rickethyo/TurnHub/Documentation/engineering/PLAYERS_AND_ACCOUNTS.md

# Players, Profiles and Accounts

Profiles, sign-in, joining a table from a phone or a Sigil, permissions and
moderation. Storage keys are in [Storage and Recovery](STORAGE_AND_RECOVERY.md);
HTTP routes are in `protocol/http-v1.md` and the route table in
`Atlas/src/web_api.cpp`.

## Profiles and sign-in

- A profile is a person: ID, name, a PIN (4-8 digits) or password (8-64
  UTF-8 bytes, no control characters), statistics and preferences. Both
  secrets travel in the same `pin` field, use the same hash
  (`profilePinHash`, a single SHA-256 over profile ID and secret) and the same
  login limiter. At most 64 profiles; new profiles need a name and secret.
- Anyone on Atlas's network can register. Signing in gives a native client
  session token (RAM only, eight-hour inactivity expiry, sent in the
  `X-TurnHub-Token` header, never in URLs). Changing the secret revokes the
  profile's other tokens. Logout removes authorization, not the participant.
- Signing in does not join the table. The authenticated profile, never a
  client-supplied player field, decides what a session may control.
- The Android app can keep one profile's secret in the Android Keystore,
  unlocked by fingerprint, face, screen lock or an app PIN, and signs in
  whenever it connects (Android 11+, `Android/README.md`). Real passkeys don't
  fit an offline Atlas (WebAuthn needs a domain name and a trusted
  certificate).

## Joining a table

- One profile has **at most one participant** at the table. Two phones and a
  Sigil may all control that participant; statistics count once.
- **Phones** join with `POST /api/session/join` and can form a whole table
  with no Sigils: pick a starter, start, play, finish, rematch.
- **Sigils** join through the **profile picker** (`profile_picker.cpp`, RAM
  browsing state only). The page lists Guest, then saved profiles, three to
  a page. E-ink: each name has a fixed key (Up/Right/Down), the click shows
  more names, Left goes back. OLED: the same page as a scrolling list. Words
  mark special rows: "no profile" (Guest), "phone sign-in" (the owner turned
  off physical use without a PIN and has no signed-in phone), "at table:
  attach" (already playing from a phone; choosing it attaches this Sigil to
  that participant). Archived or moderated profiles and profiles on another
  Sigil are not listed. Names that would look the same on a Sigil (the
  same name, or the same first 12 characters) are numbered in profile ID
  order, "Sam 1" and "Sam 2", cut to fit (2026-10-06). The picker closes after a minute idle, at game start,
  or when the Sigil joins another way.
- **Use this seat** (the app’s Players tab):
  `POST /api/session/request` with `module` and `slot`, then poll
  `GET /api/session/poll?id=` while the player chooses **Link phone** on that
  Sigil within 30 s. Signed out, approval signs the phone in to the seat's
  profile, and only for a profile without a PIN (a Sigil press proves
  possession, not the secret). Signed in, it attaches that Sigil seat to the
  signed-in profile. The app signs in from its profile list. In a lobby its Paired Sigils list
  can also request attachment of an empty seat A, with the same physical
  confirmation and server validation.
- **First phone sign-in of a PIN-less profile** (owner request 2026-10-07):
  `POST /api/session/login` for a profile with no secret saves the given PIN
  or password as its secret and signs in (log `ATLAS|PROFILE|PIN_SET_AT_SIGN_IN`).
  The app asks for it twice; from then on it is checked as usual. Anyone at
  the table can already seat a PIN-less profile from a Sigil or the tablet,
  so claiming it from a phone grants nothing new.
- **Seat B** on a shared Sigil uses the same picker (**Add seat B**); Guest
  adds seat B directly. `PickProfile` with slot 2 adds the seat and binds the
  profile in one step.
- Attachment and profile choice happen in the lobby, with one exception
  (owner request 2026-10-07, *Experimental: host-tested*): during a running
  or paused game a Sigil outside it offers **Join** while some player in the
  game has no Sigil (seated from a phone or the tablet). Its picker then lists
  only those players (no Guest), and choosing one moves that player onto the
  Sigil with their place, life and clock (`GameEngine::replaceController`).
  Nobody new joins mid-game until venue lobbies, and a participant that
  already has a physical controller is never silently moved.
- Seat bindings are temporary (RAM): released when the seat leaves (the
  Sigil's Leave, Drop seat B, a phone leaving for a profile seated on a
  Sigil, a Game Master removal), at Reset and on restart. They survive Game
  Over so Sigils can name the winner, and Rematch restores them. A seated
  Sigil that reboots keeps its profiles.
- **Turn order** is set on the Atlas touchscreen in the lobby by tapping a
  player chip: Earlier/Later (`MoveSeat`) and, on a shared Sigil, B left or
  B right (`SetSeatSide`). Any player may do it, and so may a table tablet
  (Earlier/Later, 2026-10-07); a phone may not.
  Starter, participants and bindings stay with their physical seats, and
  recovery restores A/B and B/A pairs.

## Tablet mode (2026-10-06)

*Experimental: host-tested, not yet played on hardware.* One shared tablet or
phone lies in the middle of the table, split into a panel per player that
faces their seat (Android app, Game → Open tablet mode, `ui/tablet/`).
The app renders `/api/v1/state` and sends `/api/tablet/*` requests; it keeps
the screen on and hides system bars during play. Browser tablet mode is retired.
The game selector follows Atlas’s venue list. A shared-tablet switch keeps its
players seated in their original game. State/name caches and local staged edits
reset when games change; queued offline changes include the venue game, boot
and participant identity. Native raw table actions include `expectedGame`; Atlas
rejects a stale selected-game context before dispatching the semantic action.

- **Turning it on.** A signed-in account activates tablet mode from Game.
  With the table-code setting off it activates directly; when on, prove table
  presence with `purpose=tablet` and the Atlas code, unless the account has
  Tablet access. Successful `POST /api/tablet/enable` revokes this device's
  personal token and returns a fresh RAM-only shared-tablet credential. Its
  profile ID is empty, its name is Shared tablet, and it has no personal or
  Admin permissions. It cannot join as a player, edit profiles, upload artwork,
  inspect private preferences/statistics or administer Atlas. The route allowlist
  permits game/state/seats/profile-list/artwork reads, tablet actions, game
  selection and logout. Existing player seats and other phones stay independent.
  Closing or leaving tablet mode revokes the grant and leaves the app signed
  out, including local exit while disconnected. Remote sessions expire after
  eight idle hours or restart. No personal login is restored on exit.
- **Seating.** In the lobby the tablet adds players: a new name creates a
  profile with no PIN (names are unique, ignoring case); an existing profile
  follows its owner's PIN choice below, else the tablet asks for its PIN
  (rate limited like a sign-in). Seated players join as browser controllers,
  so a Sigil can then attach to any of them through its picker ("at table:
  attach") and a phone can sign in to the same participant.
- **Turn order.** The tablet lobby's arrows move a seat earlier or later
  (`move-earlier`/`move-later`, `MoveSeat` with the `TableTablet` origin);
  panels sit clockwise in that order. The game's order is fixed once it
  starts. Claim the win and Concede sit at the top of each panel's More.
- **Acting for a seat.** Every panel action names the seat (`module`, `slot`
  from `/api/v1/state`) and goes through the same seat callbacks and Intents
  a phone uses (`web_tablet_api.cpp`). Atlas still decides: a seat changes
  only its own life, records only Commander damage it received, only the
  active player passes or claims a win, and win confirmations go to the
  confirming seat. Statistics are recorded per profile as for any game.
- **Paused decisions:** tablet clients keep the central pause overlay closed
  during a win claim so the scheduled player's panel can Confirm or Deny.
  Resume is offered only for an ordinary pause. Elimination selection directs
  the table to the existing Atlas/Sigil controls instead of offering Resume.

## Owner policy

Each profile owner chooses, in the portal or app (`POST /api/session/policy`):

- **Allow Sigil and tablet use without a PIN** (`allowPhysicalWithoutPin`).
  Off means a Sigil or a table tablet can seat that profile only while the
  same profile has a live phone session, or (tablet only) after its PIN is
  typed on the tablet. Turning it off needs a saved secret. Existing participation continues if the policy
  changes or the session expires.
- **Hide stats without authentication.** Controls visibility only; statistics
  always accumulate. Atlas enforces it before serializing anything.

Missing records keep physical play allowed and hide unauthenticated stats.
Anyone at the table can see the list of profile names, as in the portal's
sign-in list.

## Permissions

| Permission | Allows |
|---|---|
| Admin | Account permissions, device names, network settings, firmware and portal updates, pairing confirmation and forget, factory reset, Return table to lobby, speaker volume |
| Game Master | Force pass (logged as a master pass), nudge mute; optional sub-permissions **reset connections** and **remove from game** |
| Developer | Developer page, diagnostics and the RAM log download (`GET /api/diagnostics/log`) |
| Tablet access | Turns on tablet mode without a table presence code (bit 32; needs no other role) |

A normal account has none. Permissions combine freely and are checked on
Atlas for every protected request. Privileged accounts can't remove their
secret. **There is no table host** (2026-09-25): any seated player may start,
pick the starter, change next-game settings, rematch or reset.

**First Admin.** On a new Atlas the app's setup or the portal's banner lets a
signed-in account with a secret claim the first Admin, after proving
presence (below). Neither a name nor first registration grants privileges.
The first Admin can't be demoted.

**Presence at the table** (`front_panel.cpp`). Protected device actions need
proof that the account holder is at the table: the account asks for a code,
the Atlas screen shows a six-digit code and a QR code for that account only
for 90 s (`PRESENCE_CODE_MS`), and entering or scanning it verifies the
account for 10 minutes (`PRESENCE_GRANT_MS`). Five wrong codes cancel it;
**Cancel** on the screen removes a code nobody asked for; **Stop** in Device
Settings ends a grant early. Without it the request gets
`403 {"presenceRequired": true}` and the client starts the code flow. It is
needed for the first Admin, network settings, device names, firmware and
portal updates, pairing confirmation, Return table to lobby and factory reset.

**The table code is optional** (2026-10-08, after testers found the code on
every update a reason not to use TurnHub). It is **off by default**: every
signed-in account counts as at the table, so the account permission alone
decides (an Admin for everything above), and firmware still installs only
when signed and the same or newer. An Admin turns it on in Device Settings
(portal, basic portal or app), saved in NVS as `tcode`
(`table_code_setting.h`, Intent `ConfigureTableCode`). Turning it off again
needs a code that Admin actually entered, so an Admin elsewhere on the Wi-Fi
cannot quietly drop the extra step. While it is off the Atlas screen's Wi-Fi
QR code also shows a private password without a code.

## Moderation

Game Master actions go through the `Moderate` Intent, which re-checks
permission and target state:

- **Force pass** acts at once, within the normal pause and decision rules.
- **Reset connections** revokes the target's sessions and pending claims and
  suspends its Sigil controls until a PIN sign-in. Seat, life and game state
  stay. A shared Sigil is suspended as a unit.
- **Remove from game** also leaves the lobby or eliminates the participant
  through the concession flow (open decisions finish first; a primary seat
  with a seat B removes B first). The account and statistics stay.
- **Nudge mute** stops that account sending nudges (`NudgePlayer` is refused).

Both disconnecting actions need the target to have a secret. Connection
resets and removals are counted (`o<profileId>`), saved before acting
(a storage failure rejects the action), and shown only to the account's own
PIN-verified session, never to Admins, Game Masters, seats, Sigils or
exports.

Archived accounts stay visible to Admins at the bottom of the account list,
can be restored, and are hidden from Game Master tools.

## Not done yet

- A slower salted hash (PBKDF2 via mbedTLS) for PINs and passwords, and a
  larger NVS partition, since today's 20 KB likely fits only about 20 profiles
  rather than 64. Both are parked together in
  [Staged Changes](STAGED_CHANGES.md), "Parked: storage batch".
- Future LCD artwork transfer/cache and final ESP32-S3 screen layouts.
- Per-Sigil startup choice (last profile or picker).
- Moderation from the Atlas Player screen.

## Verification

Host scenarios run the real HTTP handlers, Intent handlers and engine:
registration and login (PIN and password), hardware-free games, duplicate-join
refusal, concurrent sessions, logout and re-login, PIN throttling and
revocation, mixed attachment, the picker for both seats and policies,
permissions, presence codes, moderation and counter privacy. Phone-only
games, phone plus Sigil on one player and persistence across reboots are
verified in use (owner, 2026-10-02).

## Standalone device identity and optional import

Android local players have their own UUIDs, independent of Atlas profiles.
Adding a name creates a player; selecting a saved player reuses the local ID.
Equal names remain separate. Completed matches snapshot identity/name and keep
local statistics independent of Atlas totals. History/import state belongs to
Android's local library; see [Android](../../Android/README.md) for the schema.

Optional import requires explicit per-match choices for all players on a
specific `(atlasId, profileId)` destination. Linking never renames/replaces a
local player or rewrites historical match facts. No typed-name, cached-name or
cross-Atlas matching exists. Pending mappings are frozen for retry, imported
matches cannot be submitted again by the app, and rejected records/reasons stay
visible for explicit review. Atlas validates destination hardware identity and
all exact profile identities before crediting a new record. Existing session
sign-in is still required; profile linking does not itself grant permissions.
See [import contract](../../protocol/http-v1.md#standalone-tablet-game-import-2026-10-07).

## Player artwork (2026-10-10)

*Implemented; host/build validation recorded in COLLABORATION.md; physical
acceptance pending.* Preset keys and IDs stay stable. Android uses scalable
vector masters in `design/avatars`; Atlas uses generated 64-pixel alpha masks
area-filtered into its current slot. Frozen Sigils retain their existing assets.

My account → Personalization accepts a phone-local JPEG/PNG/WebP (up to 20 MiB
and 32 megapixels). Bounded decode honors EXIF orientation, crop sliders choose
zoom and position, and Preview displays the final compressed image plus
provisional 64/128-pixel LCD previews. The phone flattens transparency on white
and produces a baseline RGB JPEG, 512 square pixels and at most 48 KiB. The
original is never uploaded. Upload/replace stores pending art on Atlas's SD;
Admin review in Players → People → person approves or rejects the specific
revision. Pending art is private to that player and Admins; approval selects it
for public app/tablet/Atlas display. Pending replacement retains approved art.
None/presets may be selected without deleting approved artwork; Remove uploaded
image removes pending/approved artwork and selects None. Refresh image approval
reloads the profile after review. Current Sigils render their ordinary fallback.

SD unavailability fails saves visibly and falls back safely for play. A checksum
or decode failure displays a neutral fallback. Artwork is outside game-state
polling; immutable image paths are cached per connection/game. Names, life totals
and controls remain separate from decorative artwork. The master is suitable for
future LCD layouts; those firmware targets and their radio transfer are pending.
