rickethyo/TurnHub/Documentation/legal/DEPENDENCY_TRACKER.md

# TurnHub Dependency and IP Tracker

This is the working tracker for third-party software, assets, trademarks, externally sourced design material, and other IP that may create attribution, licensing, or release obligations.

The goal is simple: know what entered the project, where it came from, how it is used, and what must happen before distribution.

## Status legend

- **GREEN** - permissive or tool-only dependency with straightforward obligations.
- **YELLOW** - compatible in principle, but distribution details or exact obligations still need confirmation.
- **RED** - strong copyleft, unknown license, noncommercial restriction, incompatible terms, or another issue that must be resolved before production distribution.
- **N/A** - reference/trademark/design item rather than a software license.

## Current software dependencies

| Item | Version/source currently known | Used by | License | Ships with product? | Status | Required action |
| --- | --- | --- | --- | --- | --- | --- |
| Arduino-ESP32 | PlatformIO `espressif32`, Arduino framework | Atlas + Sigil | LGPL-2.1 | Yes, firmware build | YELLOW | Confirm exact release version/components and satisfy LGPL distribution/relinking/source obligations for the chosen firmware distribution model. Preserve notices. |
| GxEPD2 | `zinggjm/GxEPD2`, current PlatformIO dependency | Sigil e-ink | GPL-3.0 | Yes if current Sigil firmware ships | RED | Decide before production whether to comply with GPLv3 for the resulting firmware or replace with a suitably licensed display driver. Legal review before commercial release. |
| Adafruit GFX Library | Transitive GxEPD2 / SH110X dependency | Sigil e-ink and OLED graphics | BSD-style | Yes if linked into shipped firmware | GREEN | Preserve copyright, conditions, and disclaimer in release notices/materials as required. |
| LovyanGFX | `lovyan03/LovyanGFX@1.2.30` (PlatformIO) | Atlas TFT (E32R28T) | FreeBSD (BSD-2-Clause) for LovyanGFX. Bundled Adafruit (BSD) and Bodmer (FreeBSD) code carries its own notices | Yes, Atlas firmware | GREEN | Preserve the combined notices in `license.txt` in release materials. Atlas uses LovyanGFX's DejaVu fonts (Bitstream Vera-style license) and glcd font, plus its own Brass fonts (Cinzel/Oswald, row below); do not use the bundled GNU FreeFont `Free*` fonts (GPL with font exception) without review. |
| Cinzel and Oswald fonts (Brass display theme) | Cinzel 2.000 static Bold/Black ([NDISCOVER/Cinzel](https://github.com/NDISCOVER/Cinzel)) and Oswald 4.103 SemiBold ([googlefonts/OswaldFont](https://github.com/googlefonts/OswaldFont)), both fetched from Google Fonts; rendered to bitmaps by `tools/fonts/make_fonts.py` into `Atlas/include/brass_fonts.h` and `Sigil/include/brass_fonts.h` (2026-09-29). The TTFs are not committed | Atlas TFT, Sigil e-ink and OLED text | SIL Open Font License 1.1 (text and copyright lines in `tools/fonts/OFL.txt`) | Yes, embedded bitmaps in both firmwares | GREEN | Embedding in firmware is allowed. Keep `tools/fonts/OFL.txt` with the source and include its copyright lines and license in release notices. Never sell the fonts by themselves. Neither font declares a Reserved Font Name. |
| Inter and Cinzel variable fonts (V1 design system) | Inter 4 `Inter[opsz,wght].ttf` and Cinzel `Cinzel[wght].ttf` from [google/fonts](https://github.com/google/fonts) (`ofl/inter`, `ofl/cinzel`), fetched 2026-10-02, subset to Latin with fontTools; committed as `design/fonts/*.ttf` and `*.woff2` (see `design/README.md`) | Android app, and Inter bitmap text in Atlas/Sigil firmware (`tools/fonts/make_modern_fonts.py`, 2026-10-09) | SIL Open Font License 1.1 (`design/fonts/OFL-Inter.txt`, `design/fonts/OFL-Cinzel.txt`) | Yes, APK and firmware bitmaps | GREEN | Ship the OFL texts with app open-source notices and firmware notices. The admin portal uses system fonts. Subsetting creates a Modified Version; neither font declares a Reserved Font Name, so the family names may stay. Never sell the fonts by themselves. |
| Adafruit SH110X | `adafruit/Adafruit SH110X@2.1.15`, [upstream](https://github.com/adafruit/Adafruit_SH110x) | Optional Sigil OLED environment only | BSD-3-Clause ([license](https://github.com/adafruit/Adafruit_SH110x/blob/master/license.txt)) | Yes if OLED firmware ships | GREEN | Preserve upstream copyright, license, disclaimer and required source notices in release materials; the vendor splash is disabled in the build. |
| Adafruit NeoPixel | `adafruit/Adafruit NeoPixel@1.15.5`, [upstream](https://github.com/adafruit/Adafruit_NeoPixel) | Sigil E-ink build (`sigil` env) status ring only | LGPL-3.0 ([license](https://github.com/adafruit/Adafruit_NeoPixel/blob/master/COPYING)) | Yes if E-ink Sigil firmware ships | YELLOW | Statically linked, so LGPL-3.0 requires letting recipients relink against a modified library (e.g. provide object files or the full source) and preserving notices. Covered by the same pre-release review as GxEPD2 (GPL-3.0) in the same firmware. |
| Mbed TLS | 2.28.7, bundled inside Arduino-ESP32 (framework-arduinoespressif32 2.0.17); no separate PlatformIO dependency | Atlas + Sigil secure link (X25519, AES-128-CCM, HMAC-SHA256; `shared/include/secure_link_mbedtls.h`, 2026-09-28) | Apache-2.0 (upstream also offers GPL-2.0-or-later; Espressif ships it under Apache-2.0) | Yes, linked into both firmwares | GREEN | Preserve the Apache-2.0 license and NOTICE in release materials with the other Arduino-ESP32 notices. TurnHub calls its primitives only; no mbedTLS source is copied into the repository. The RFC test vectors in `secure_link.h` are published values from RFC 7748, 4231 and 3610. |
| Adafruit BusIO | Transitive GFX / SH110X dependency | Sigil graphics bus support | MIT ([license](https://github.com/adafruit/Adafruit_BusIO/blob/master/LICENSE)) | Yes if linked into shipped firmware | GREEN | Preserve copyright and license notice. |
| PlatformIO Core | Build environment | Development | Apache-2.0 | No, currently build tooling only | GREEN | Track tool version for reproducibility. No product notice expected unless redistributed. |
| Python `cryptography` | 46.0.7 (pip in CI; locally the copy bundled with PlatformIO's esptool) | `tools/firmware/thfw.py`: signs and checks OTA packages (2026-09-29) | Apache-2.0 or BSD-3-Clause | No, developer and CI tooling only | GREEN | Not shipped. The signatures it makes are verified on the devices by Mbed TLS and in the app by `java.security`. |
| GitHub Actions: checkout, setup-python, setup-java, upload-artifact | Official `actions/*` repositories; exact commit revisions in `.github/workflows/ci.yml` | Development CI only | MIT (upstream `LICENSE` in each action repository) | No, not embedded in firmware or APK | GREEN | Preserve upstream notices if action code is ever redistributed. Workflow invokes the actions without copying their implementation into TurnHub. |
| GitHub Action: r0adkll/upload-google-play | `r0adkll/upload-google-play` v1.1.5, pinned to commit `e738b9dd8f2476ea806d921b64aacd24f34515a5` in `.github/workflows/ci.yml` | Development CI only: publishes master's Android bundle to Play internal testing | MIT (upstream `LICENSE`) | No, not embedded in firmware or APK | GREEN | Receives the Play service account key at run time; keep it pinned to a reviewed commit. |
| wokwi-ws29v2-custom-chip | `bonnyr/wokwi-ws29v2-custom-chip` release v0.0.5 `chip.zip` (`chip.wasm` SHA-256 `6f59d1873e3faa07a018a088f61b1ffff6a8bcfebf7925eadd7e2082dd318d9d`), vendored as `Sigil/wokwi/chips/epaper-2in13.chip.wasm` with a TurnHub `chip.json` (2.13" geometry) | Sigil Wokwi simulation only | MIT (copy in `Sigil/wokwi/chips/LICENSE-wokwi-ws29v2-custom-chip.txt`) | No, development simulation only | GREEN | Keep the license file with the binary. Not linked into firmware. |
| org.json (JSON-java) | `org.json:json:20260814`, Android `testImplementation` only | Android JVM unit tests (the app itself uses Android's built-in `org.json`) | Public Domain (per its Maven POM) | No, test classpath only | GREEN | None while test-only. Re-review if it ever moves to an `implementation` dependency. |
| AndroidX CameraX (`camera-camera2`, `camera-lifecycle`, `camera-view`) | `androidx.camera:*:1.5.0` | Android app: Admin-code QR scanner preview | Apache-2.0 | Yes, Android APK | GREEN | Include the Apache-2.0 license and any NOTICE text in the app's open-source notices. Camera use is optional and asked for only when the player taps Scan. |
| ZXing core | `com.google.zxing:core:3.5.3`, [upstream](https://github.com/zxing/zxing) | Android app: on-device QR decoding (no network) | Apache-2.0 | Yes, Android APK | GREEN | Include the Apache-2.0 license and NOTICE in the app's open-source notices. |

## Platform/toolchain follow-up

Optional Windows native-test compiler: PlatformIO package
`platformio/toolchain-gccmingw32` 1.50100.0 (GCC 5.1.0), used by
`Atlas/tests/host/run-gcc.ps1`. Installed package provenance is recorded in its
`package.json`; component license texts are in its `licenses/` directory.
This is development-only tooling, not linked into ESP32 firmware. Compiler and
native test binaries are not committed or distributed. Review the package's
component/runtime redistribution terms before distributing either; MSVC remains
an alternative via `run.cmd`.

The high-level rows above are not yet a complete software bill of materials. Before release, generate the dependency list from the exact production builds and inventory:

- Espressif SDK/framework components pulled into Atlas firmware.
- Espressif SDK/framework components pulled into Sigil firmware.
- Any binary blobs, bootloaders, partition tools, OTA components, crypto libraries, or other linked code included by the toolchain.
- Android application dependencies once the native client is created.
- Any future BLE, QR, image, persistence, networking, or serialization libraries.

## Assets and externally sourced material

| Item | Current state | Status | Rule |
| --- | --- | --- | --- |
| Web UI fonts | Admin portal: system fonts; Android app: Inter and Cinzel, recorded under software dependencies | GREEN | Keep the OFL texts with app notices; the portal embeds no web fonts. |
| Web UI icons/images | No external icon/image package identified in current ESP32 portal | GREEN | Do not paste icons/art from another product. Record any future asset pack before use. |
| V1 icon set and brand mark | Original line icons drawn for TurnHub on 2026-10-02 (`design/icons/*.svg`) and an original turn-arrow mark; no third-party icon set | GREEN | Keep new icons original; record the source of any icon that is not. |
| Sigil display graphics | Programmatic geometry (gears, rivets, gauges) plus the Cinzel/Oswald bitmap fonts recorded above; no third-party art identified | GREEN | Continue using original/programmatic assets unless a licensed source is recorded. |
| Sounds/tones | Programmatic buzzer tones; no sampled third-party audio identified | GREEN | Record any future audio file, sound pack, or melody source and license. |
| CAD/enclosure files | No external production enclosure asset recorded in this tracker | GREEN | If a downloaded 3D model is used or modified, record source and model license before committing/shipping it. |
| Schematics/reference designs | No third-party schematic copied into the production tree is currently recorded | GREEN | Record vendor/reference-design source and applicable terms if incorporated. |

## Trademark and compatibility references

| Reference | Current use | Status | Required action |
| --- | --- | --- | --- |
| Magic: The Gathering / MTG | Game profile/compatibility wording in documentation and legacy UI | N/A | Keep use descriptive. Avoid logos, card art, mana symbols, card frames, or implication of affiliation. Review commercial wording before launch. |
| Commander / MTG Commander | Game profile and commander-damage terminology | N/A | Same as above. Review exact naming/disclaimer strategy before public commercial release. |
| Yu-Gi-Oh! | Game profile/compatibility wording | N/A | Keep descriptive and avoid branded visual assets or implied endorsement. Review before launch. |

## Open IP/legal tasks

- [ ] Resolve GxEPD2 GPLv3 strategy before any commercial Sigil firmware distribution.
- [ ] Correct the placeholder `[year] [fullname]` in the root `LICENSE.txt` and confirm the intended license scope.
- [ ] Produce an exact production SBOM/dependency manifest from Atlas and Sigil release builds.
- [ ] Add complete required upstream license texts/notices to the release package.
- [ ] Review trademark compatibility wording before Kickstarter, retail packaging, app-store publication, or paid promotion.
- [ ] Add Android dependencies here as soon as the native project is generated.
- [ ] Perform a final third-party asset audit before public release.

## Change log

### 2026-09-28 (GitHub Actions)

Recorded the four official GitHub actions used for checkout, language setup and
development artifact retention. They run on GitHub-hosted build machines and do
not add a device/runtime dependency.

### 2026-09-25 (Sigil status ring)

Added Adafruit NeoPixel (LGPL-3.0) for the E-ink Sigil's Jewel 7 status ring.
No third-party code was copied into the tree.

### 2026-09-24 (Sigil OLED scaffold)

Added the optional SH110X driver, recorded BusIO and extended the GFX usage
record. No third-party implementation code or photo was copied into the tree.

### 2026-09-24 (Atlas display)

Added LovyanGFX for the Atlas E32R28T TFT, and recorded the font restriction.

### 2026-09-24

Added the test-only `org.json:json` dependency introduced with the Android live-Atlas integration. The broader Android dependency inventory (AndroidX, Compose, coroutines, JUnit) remains the open task above.

### 2026-09-19

Initial tracker created from the current `intent-android-foundation` branch. Known direct dependencies and current game-name compatibility references were inventoried. GxEPD2 was marked RED for production review because the current Sigil firmware directly uses it under GPLv3.

### Artwork build tools (2026-10-10)

CairoSVG 2.8.2 (LGPL-3.0-or-later) and Pillow 11.3.0 (HPND/Pillow license)
are development-only rasterization tools pinned in `tools/artwork-requirements.txt`.
They generate alpha masks from TurnHub's original SVG artwork and are not linked
or bundled into Atlas or Android. CI provenance checking uses stdlib only.
No third-party artwork or new production image/crop library is introduced.
