rickethyo/TurnHub/PRIVACY.md

# TurnHub Privacy Policy

Effective 7 October 2026. This policy covers the TurnHub Android app
(`com.turnhub.android`) and the TurnHub table hardware it controls.

## The short version

TurnHub does not collect your data. The app has no ads, analytics, tracking
or crash reporting, and TurnHub runs no servers. Everything you enter stays on
your phone or on your own TurnHub table controller (the "Atlas").

## What the app stores and where

- **On your Atlas.** Your profile name, a PIN or password (stored hashed),
  game settings, accessibility preferences and game statistics live on the
  Atlas, which sits at your table. The app reaches it only over the Atlas's own
  Wi-Fi network. Nothing on the Atlas is sent to us or to anyone else. Whoever
  administers that Atlas can remove profiles or factory-reset it, which erases
  this data.
- **On your phone.** The app remembers the Atlas Wi-Fi password and, if you
  turn on automatic sign-in, your profile's PIN or password. That secret is
  encrypted with a key Android releases only after your fingerprint, face or
  screen lock. Uninstalling the app or clearing its storage removes it.

## Permissions

- **Camera:** scans the QR codes TurnHub shows during setup. Images are
  processed on the phone and never stored or sent.
- **Nearby devices / local network and Wi-Fi state:** finds and joins your
  Atlas's Wi-Fi network.
- **Biometrics:** unlocks your saved sign-in, if you turn that on.
- **Notifications and foreground service:** shows table status and keeps the
  connection to the Atlas while a game is running.
- **Internet:** used only to download TurnHub firmware updates.

## Firmware updates

To check for and download firmware updates, the app requests public files from
TurnHub's GitHub releases. GitHub receives the request (including your IP
address) under [GitHub's privacy statement](https://docs.github.com/site-policy/privacy-policies/github-general-privacy-statement).
No account or personal data is included.

## Children

TurnHub is not directed at children under 13 and does not knowingly collect
personal information from anyone.

## Changes and contact

Changes to this policy are published here, with a new effective date. Questions
go to the developer contact email on TurnHub's Google Play listing, or open an
issue at <https://github.com/rickethyo/TurnHub/issues>.
