rickethyo/TurnHub/Documentation/User Manual/TurnHub Manual V0.1.docx

# TurnHub User Manual

## Prototype Edition v0.1

TurnHub is a tabletop turn management system designed to keep the game moving without putting a phone in the middle of the table.

The system consists of a central Atlas and one or more player Sigils. Atlas maintains the authoritative game state while Sigils give each player a simple physical interface for turns, life totals, actions, and other game events.

Prototype Notice
This manual describes the current TurnHub prototype. Controls, menus, terminology, and hardware may change before the final production version.

# 1. Meet TurnHub

## Atlas

Atlas is the central controller for the table.

It is responsible for:

- Maintaining the current game state
- Tracking whose turn it is
- Managing connected Sigils
- Handling game-wide actions
- Hosting the TurnHub web interface
- Coordinating turn, life, pause, win, and elimination events

Atlas is the authority for the game. Sigils and browser clients send requests to Atlas, which determines and distributes the resulting game state.

## Sigils

Sigils are the player-facing devices placed around the table.

Depending on the current prototype configuration, a Sigil can display information such as:

- Player identity
- Current turn status
- Life total
- Game status
- Pairing status
- Alerts and prompts

A single Sigil can support up to two players.

## Virtual Sigils

A phone, tablet, or computer can also participate through the TurnHub browser interface.

Virtual Sigils provide many of the same player functions without requiring an additional physical module.

# 2. Before You Begin

For a typical game you will need:

- One TurnHub Atlas
- One or more Sigils, or browser-based Virtual Sigils
- Power for Atlas
- Power or sufficient battery charge for each physical Sigil
- A phone, tablet, or computer for initial setup when desired, although play can begin without first adding profiles, assigning an administrator role, or ever interacting with the web portal. Note: Player identifications will be limited to “Player 1” “Player 2” etc. when no profiles have been preset. Statistics for these “Player” profiles are not saved.

TurnHub is designed to operate locally and does not require an Internet connection for normal game operation.

# 3. Starting TurnHub

## Power On Atlas

Connect power to Atlas and allow it to start.

Atlas will initialize its game services and make the TurnHub interface available.

Do not begin pairing devices until Atlas has finished starting.

## Power On Your Sigils

Turn on each Sigil you plan to use.

A Sigil that has not yet joined the current Atlas will indicate that it is waiting for a connection or pairing.

# 4. Connecting to Atlas

TurnHub uses a local interface for game setup and management.

Players can join using:

- A QR code
- The local TurnHub address
- A previously configured connection method

The QR code can be displayed or printed for repeated use with the same table setup.

Opening the TurnHub page provides access to the available player and game controls.

# 5. Pairing a Physical Sigil

Atlas and Sigils include a dedicated Pair control.

## To Pair a Sigil

1. Press the Pair button on Atlas.
2. Atlas opens a pairing window for approximately 30 seconds.
3. Press the Pair button on the Sigil you want to connect.
4. Wait for the pairing confirmation.
5. Repeat for additional Sigils as needed.

Status indicators show when pairing is in progress and when a device has successfully joined.

Pairing acknowledgements are intentionally limited so TurnHub does not repeatedly generate unnecessary alerts during normal play.

# 6. Player Setup

Players can create or select a profile before beginning a game.

Profiles may include:

- Player name
- Avatar
- PIN
- Personal settings

Profiles are separate from physical Sigils. A player is not permanently assigned to one device.

This means the same Sigil can be used by different players in different games.

## Two Players on One Sigil

A Sigil can support two players.

When a second player is added, TurnHub provides a distinct indication so everyone at the table can tell that the device is representing more than one player.

# 7. Starting a Game

From the TurnHub interface:

1. Confirm that all expected players are connected.
2. Select or create player profiles.
3. Configure the game.
4. Choose the appropriate starting life total if life tracking is being used.
5. Start the game.

Currently supported starting life totals include:

- 20
- 25
- 40
- 2000

Additional game-specific values may be supported as TurnHub development continues.

# 8. Taking Turns

TurnHub always maintains a current active player.

The active player's Sigil provides a clear indication that it is their turn.

When finished, use the appropriate turn control to pass play to the next player.

Atlas updates the game state and notifies the affected Sigils.

## Passing to Yourself

TurnHub supports passing a turn back to yourself when required by the game or table rules.

A distinct alert is used for a self-pass so it is not easily confused with normal turn progression.

# 9. Sigil Controls

The current Sigil design uses:

- Two primary controls
- One secondary action control
- One dedicated Pair control

Final button labels and iconography may change before production.

## Action Control

The secondary control supports more than one function.

Short press: Action Long
Long press: Claim Win

These behaviors may be renamed or reassigned as the physical control layout is finalized.

## Pair Control

The Pair control is reserved for device pairing and connection management.

This keeps pairing separate from normal gameplay and helps prevent accidental device changes during a game.

# 10. Life Tracking

When life tracking is enabled, players can adjust life totals through TurnHub.

For supported Magic-style configurations, TurnHub includes larger adjustment options such as:

+10 and -10

Other players may also request changes to another player's life total.

When this occurs, TurnHub displays a confirmation prompt.

If no response is made, the current prototype can automatically confirm the change after approximately 30 seconds.

# 11. Commander Damage

TurnHub can track Commander damage separately from the player's main life total.

This allows players to monitor Commander-specific damage without replacing normal life tracking.

Because game formats vary, players remain responsible for determining when a game rule requires elimination.

# 12. Pausing the Game

TurnHub includes a global pause function.

When paused:

- Normal turn progression is suspended
- Players can resolve questions or interruptions without losing the current game state
- The game can resume from the same position afterward

This can be useful for rules discussions, food breaks, disconnected hardware, or other interruptions.

# 13. Nudges and Alerts

Players can send a nudge when another player needs attention.

TurnHub can provide alerts through:

- Sigil indicators
- Audio feedback
- Browser-based buzzer notifications

Alerts are designed to communicate useful events without turning the table into a constant stream of sounds and lights.

# 14. Claiming a Win

A player can submit a Claim Win request.

A win claim does not immediately end the game.

Instead, TurnHub asks the remaining living players to approve the result.

All required players must approve the claim.

If a player denies the request, the win claim is cancelled and normal play continues.

This helps prevent an accidental button press from ending the game.

# 15. Conceding

A player who is leaving the game can concede.

Conceding removes that player from normal turn progression while preserving the rest of the game.

Earlier prototype versions may refer to this function as Eliminate. Current terminology uses Concede for a player intentionally leaving the game.

# 16. Browser Interface

Atlas provides a local browser interface for setup and game management.

Available functions may include:

### Game

- Join game
- Start game
- Leave game
- View current players
- Manage turn state
- Adjust life
- Pause and resume
- Claim a win
- Concede
- Send nudges

### Player

- Select profiles
- Edit player information
- Choose avatars
- Enter a profile PIN

### System

- View Atlas status
- Restart Atlas
- Shut down Atlas

Some administrative functions may require elevated permissions.

# 17. Game Master Access

TurnHub supports a privileged Game Master or super-user role.

The Game Master can access functions that normal players may not need during ordinary play.

This role is intended for:

- Table setup
- Game administration
- Correcting unusual game states
- Troubleshooting
- Organized play environments

Exact permissions are still being refined for the prototype.

# 18. Reconnecting

If a Sigil or browser client temporarily disconnects, TurnHub attempts to restore it without requiring the game to restart.

Because Atlas owns the authoritative game state, a reconnecting player receives the current state from Atlas rather than relying on potentially outdated information stored on the client.

If a device does not reconnect automatically:

1. Confirm Atlas is still powered on.
2. Confirm the device is within range.
3. Reopen the TurnHub browser page or restart the Sigil.
4. Pair the Sigil again if required.

Do not restart Atlas unless normal reconnection attempts fail.

# 19. Restarting Atlas

Restarting Atlas may be useful after a configuration change or troubleshooting event.

Use the Restart command from the System interface when possible.

Avoid disconnecting power while Atlas is actively writing configuration or game data.

# 20. Shutting Down

For a normal shutdown:

1. End or leave the current game.
2. Open the TurnHub System page.
3. Select Shut Down.
4. Wait for Atlas to complete shutdown.
5. Disconnect power if desired.

Physical shutdown behavior may change as the production Atlas hardware is finalized.

# 21. Privacy and Local Operation

TurnHub is designed around local-first operation.

Normal tabletop gameplay does not require game data to be sent to an external service.

Features involving statistics or potentially sensitive player information are intended to be opt-in.

TurnHub's goal is to help manage the table without requiring players to hand over unnecessary personal data.

# 22. Troubleshooting

## My Sigil Will Not Pair

- Confirm Atlas is powered on.
- Press Pair on Atlas again.
- Pair the Sigil within the 30-second pairing window.
- Move the Sigil closer to Atlas.
- Restart the Sigil if necessary.

## My Sigil Disconnected

Allow the device a moment to reconnect.

If it does not:

- Confirm Atlas is still available.
- Restart the Sigil.
- Pair it again if requested.

The game state should remain controlled by Atlas.

## The Wrong Player Has the Turn

Use the available game controls to correct the active player.

If normal player controls cannot resolve the problem, use Game Master access.

## A Player Accidentally Claimed a Win

Other players can deny the win request.

A denied request cancels the claim and returns the game to normal play.

## Someone Changed My Life Total

Life changes requested by another player display a confirmation prompt.

Review the requested change before accepting it.

## The Browser Buzzer Does Not Make Sound

Some browsers prevent websites from playing audio before the user has interacted with the page.

Tap or click the TurnHub interface once, then try again.

# 23. Prototype Limitations

The current TurnHub prototype is still under active development.

You may encounter:

- Temporary interface elements
- Changing terminology
- Unfinished enclosure designs
- Features that move between software versions
- Different behavior between physical and Virtual Sigils
- Diagnostic controls not intended for the final product

Prototype users should report unexpected behavior with as much detail as possible.

Helpful information includes:

- What you were doing
- Which player was active
- Which Sigil was involved
- What you expected to happen
- What actually happened
- Whether the issue could be reproduced

# 24. The TurnHub Philosophy

TurnHub is not intended to play the game for you.

It is intended to quietly handle the bookkeeping that gets in the way of playing.

TurnHub should answer the question:

“Whose turn is it again?”

Then get out of the way.

## TurnHub Prototype Documentation

Manual Version: 0.1
Hardware: Prototype
Software: Development Build
**Product names and specifications subject to change.
