rickethyo/TurnHub/Atlas/src/profile_store.cpp

#include "avatars.h"
#include "avatar_artwork.h"
#include "profile_store.h"
#include "account_access.h"

#include "optional_preferences.h"
#include "nvs_blob_store.h"
#include "profile_stats_storage.h"
#include <esp_system.h>
#include <string.h>

namespace TurnHubProfiles {
namespace {

constexpr char PREF_NAMESPACE[] = "turnhub";

TurnHub::OptionalPreferences preferences;
TurnHubStorage::NvsBlobStore statsStorage;
// The microSD card's store for luxury records, or nullptr (limp mode).
TurnHubStorage::BlobStore *luxuryStore = nullptr;
bool preferencesReady = false;
constexpr uint8_t TRANSIENT_SEAT_CAPACITY = 16;
struct TransientSeatBinding {
  bool used = false;
  uint8_t mac[6] = {};
  uint8_t slot = 0;
  String profileId;
};
TransientSeatBinding transientSeats[TRANSIENT_SEAT_CAPACITY];

TransientSeatBinding *transientSeatFor(const uint8_t mac[6], uint8_t slot, bool create) {
  for (auto &binding : transientSeats) {
    if (binding.used && binding.slot == slot && memcmp(binding.mac, mac, 6) == 0) return &binding;
  }
  if (!create) return nullptr;
  for (auto &binding : transientSeats) {
    if (!binding.used) {
      binding.used = true;
      binding.slot = slot;
      memcpy(binding.mac, mac, 6);
      binding.profileId = String();
      return &binding;
    }
  }
  return nullptr;
}

String deviceNameKey(const uint8_t mac[6]) {
  char key[14];
  snprintf(
      key,
      sizeof(key),
      "d%02X%02X%02X%02X%02X%02X",
      mac[0], mac[1], mac[2], mac[3], mac[4], mac[5]);
  return String(key);
}

String profileKey(char prefix, const String &profileId) {
  String key;
  key.reserve(1 + PROFILE_ID_LENGTH);
  key += prefix;
  key += profileId;
  return key;
}

bool validProfileId(const String &profileId) {
  TurnHubIdentity::ProfileId parsed;
  return profileId.length() == PROFILE_ID_LENGTH &&
      TurnHubIdentity::ProfileId::parse(profileId.c_str(), parsed);
}

String makeProfileId() {
  char id[PROFILE_ID_LENGTH + 1];
  snprintf(id, sizeof(id), "%08lX", static_cast<unsigned long>(esp_random()));
  return String(id);
}

bool ensureMarker(const String &profileId) {
  if (!preferencesReady || !validProfileId(profileId)) {
    return false;
  }
  const String markerKey = profileKey('m', profileId);
  if (preferences.isKey(markerKey.c_str())) {
    return true;
  }
  return preferences.putUChar(markerKey.c_str(), 1) != 0;
}

}  // namespace

bool begin() {
  if (preferencesReady) {
    return true;
  }
  preferencesReady = preferences.begin(PREF_NAMESPACE, false);
  return preferencesReady;
}

bool ready() {
  return preferencesReady;
}

String createProfile() {
  if (!preferencesReady && !begin()) {
    return String();
  }

  for (uint8_t attempt = 0; attempt < 16; ++attempt) {
    const String profileId = makeProfileId();
    if (!profileExists(profileId) && ensureMarker(profileId)) {
      return profileId;
    }
  }
  return String();
}

bool profileExists(const String &profileId) {
  if (!preferencesReady || !validProfileId(profileId)) {
    return false;
  }
  return preferences.isKey(profileKey('m', profileId).c_str());
}

size_t listProfileIds(char (*ids)[PROFILE_ID_LENGTH + 1], size_t capacity) {
  if (!preferencesReady || ids == nullptr) return 0;
  size_t count = 0;
  nvs_iterator_t it = nvs_entry_find("nvs", PREF_NAMESPACE, NVS_TYPE_U8);
  while (it != nullptr && count < capacity) {
    nvs_entry_info_t info;
    nvs_entry_info(it, &info);
    if (info.key[0] == 'm' && validProfileId(String(info.key + 1))) {
      // Older display syncs created marker-only profiles for unused seats.
      // Keep their records/bindings intact, but do not let these placeholders
      // crowd out real accounts or exhaust the registration limit.
      const String id(info.key + 1);
      bool configured = false;
      for (const char prefix : {'n', 'p', 's', 'a', 'u', MODERATION_STATS_PREFIX, ACCESSIBILITY_PREFIX}) {
        configured = configured || preferences.isKey(profileKey(prefix, id).c_str());
      }
      if (configured) memcpy(ids[count++], info.key + 1, PROFILE_ID_LENGTH + 1);
    }
    it = nvs_entry_next(it);
  }
  nvs_release_iterator(it);
  return count;
}

String createProfileWithCredentials(const String &name, const String &pin, PinHasher hasher) {
  if ((!preferencesReady && !begin()) || name.length() == 0 || name.length() > 32 || hasher == nullptr) return String();
  char ids[MAX_LOGIN_PROFILES][PROFILE_ID_LENGTH + 1];
  if (listProfileIds(ids, MAX_LOGIN_PROFILES) >= MAX_LOGIN_PROFILES) return String();
  for (uint8_t attempt = 0; attempt < 16; ++attempt) {
    const String id = makeProfileId();
    if (profileExists(id)) continue;
    const String hash = hasher(id, pin);
    if (hash.length() != 64) return String();
    const String nameKey = profileKey('n', id), pinKey = profileKey('p', id);
    // Publish the profile marker last. Partial setup is never a login identity.
    if (preferences.putString(nameKey.c_str(), name) > 0 &&
        preferences.putString(pinKey.c_str(), hash) > 0 && ensureMarker(id)) return id;
    preferences.remove(nameKey.c_str());
    preferences.remove(pinKey.c_str());
    return String();
  }
  return String();
}

// A named profile with no PIN, as a table tablet seats a new player.
String createProfileWithName(const String &name) {
  if ((!preferencesReady && !begin()) || name.length() == 0 || name.length() > 32) return String();
  char ids[MAX_LOGIN_PROFILES][PROFILE_ID_LENGTH + 1];
  if (listProfileIds(ids, MAX_LOGIN_PROFILES) >= MAX_LOGIN_PROFILES) return String();
  for (uint8_t attempt = 0; attempt < 16; ++attempt) {
    const String id = makeProfileId();
    if (profileExists(id)) continue;
    const String nameKey = profileKey('n', id);
    // Publish the profile marker last, as createProfileWithCredentials does.
    if (preferences.putString(nameKey.c_str(), name) > 0 && ensureMarker(id)) return id;
    preferences.remove(nameKey.c_str());
    return String();
  }
  return String();
}

String nameForProfile(const String &profileId) {
  if (!preferencesReady || !profileExists(profileId)) {
    return String();
  }
  return preferences.getString(profileKey('n', profileId).c_str(), "");
}

bool setNameForProfile(const String &profileId, const String &name) {
  if (!preferencesReady || !profileExists(profileId)) {
    return false;
  }
  const String key = profileKey('n', profileId);
  if (name.length() == 0) {
    preferences.remove(key.c_str());
    return true;
  }
  if (preferences.getString(key.c_str(), "") == name) return true;
  return preferences.putString(key.c_str(), name) > 0;
}

String storedPinHashForProfile(const String &profileId) {
  if (!preferencesReady || !profileExists(profileId)) {
    return String();
  }
  return preferences.getString(profileKey('p', profileId).c_str(), "");
}
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
